NikolaTotev/Teensy-Balance-Bot-Mk_1/Documentation/Documentation Images/Microduino.png

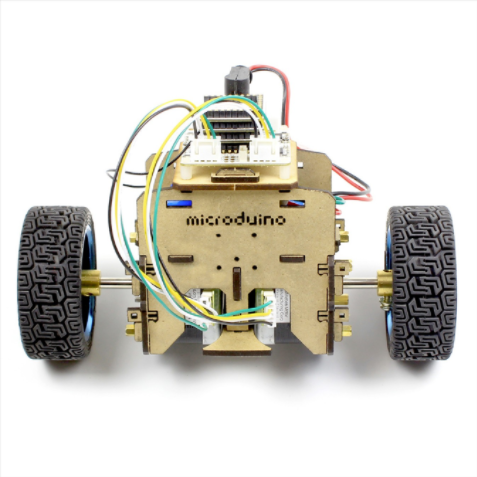
Documentation/Documentation Images/Microduino.png
