NikolaTotev/Teensy-Balance-Bot-Mk_1/Documentation/Images/Github_Cover.png

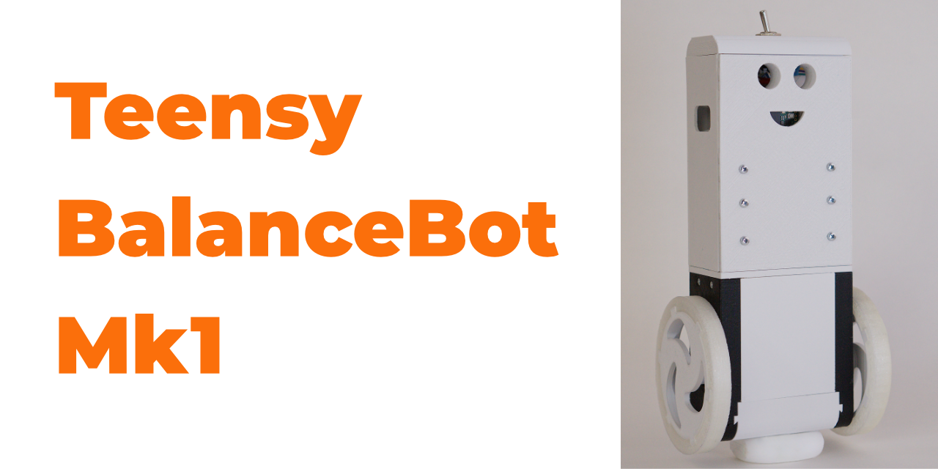
Documentation/Images/Github_Cover.png
