NikolaTotev/Teensy-Balance-Bot-Mk_1/Documentation/Presentation Images/3D Model.png

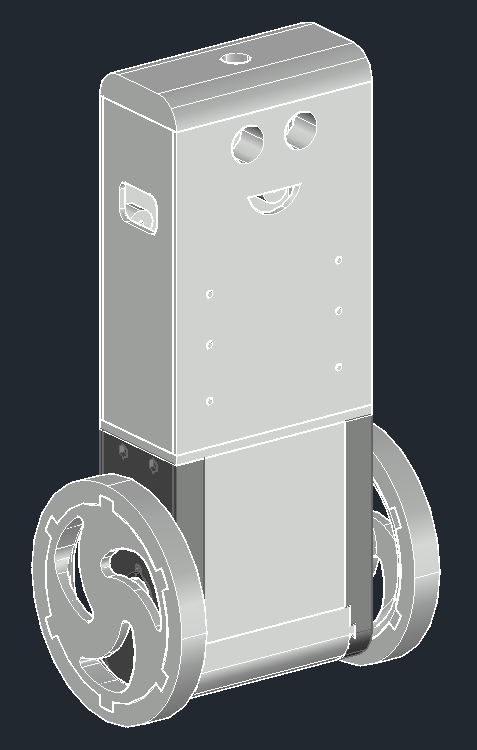
Documentation/Presentation Images/3D Model.png
