NikolaTotev/Teensy-Balance-Bot-Mk_1/Documentation/Presentation Images/2021-02-09 13_29_29-Pololu - Magnetic Encoder Pair Kit for Micro Metal Gearmotors, 12 CPR, 2.7-18V.png

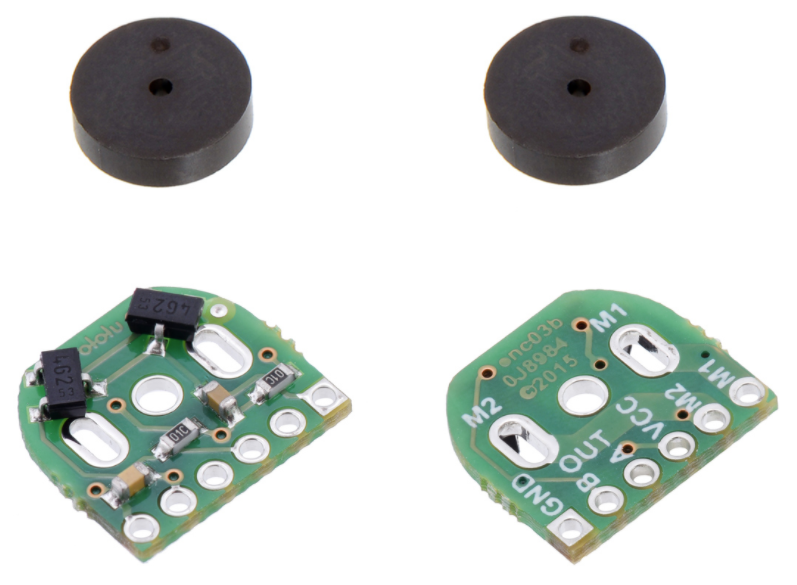
Documentation/Presentation Images/2021-02-09 13_29_29-Pololu - Magnetic Encoder Pair Kit for Micro Metal Gearmotors, 12 CPR, 2.7-18V.png
