NikolaTotev/Teensy-Balance-Bot-Mk_1/Documentation/Presentation Images/add_3_blue_1.png

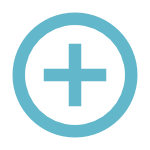
Documentation/Presentation Images/add_3_blue_1.png
