NikolaTotev/Teensy-Balance-Bot-Mk_1/Documentation/Presentation Images/Analysis.png

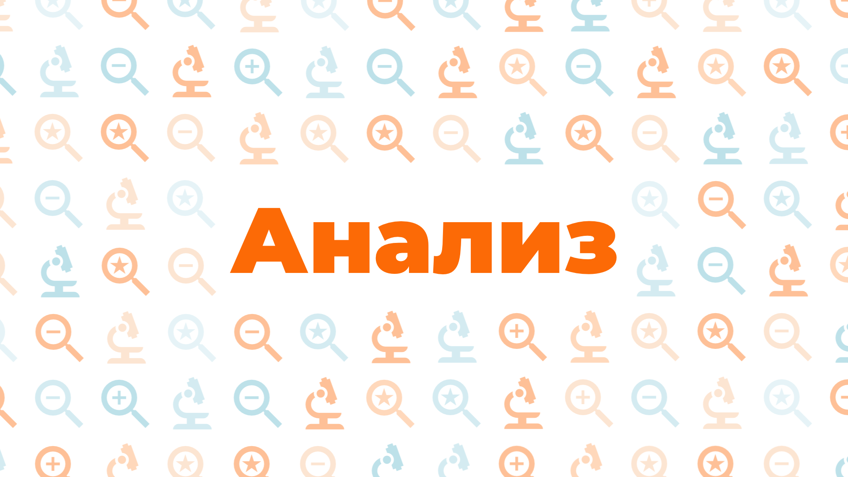
Documentation/Presentation Images/Analysis.png
