NikolaTotev/Teensy-Balance-Bot-Mk_1/Documentation/Presentation Images/Anl_Orange_1.png

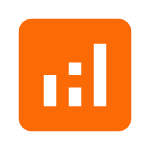
Documentation/Presentation Images/Anl_Orange_1.png
