NikolaTotev/Teensy-Balance-Bot-Mk_1/Documentation/Presentation Images/Batteries.png

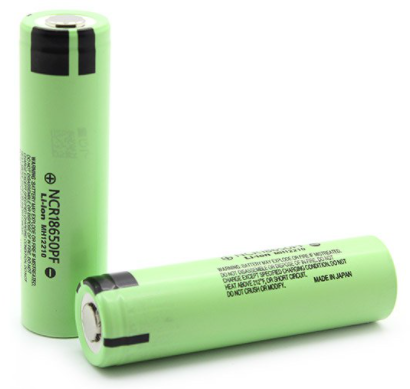
Documentation/Presentation Images/Batteries.png
