NikolaTotev/Teensy-Balance-Bot-Mk_1/Documentation/Presentation Images/Brand_Visual_Studio_Win_2019.png

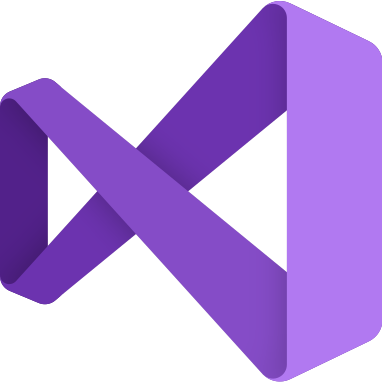
Documentation/Presentation Images/Brand_Visual_Studio_Win_2019.png
