NikolaTotev/Teensy-Balance-Bot-Mk_1/Documentation/Presentation Images/Calc_Orange_1.png

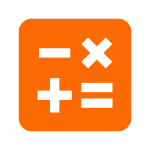
Documentation/Presentation Images/Calc_Orange_1.png
