NikolaTotev/Teensy-Balance-Bot-Mk_1/Documentation/Presentation Images/Check_Check_Blue_1.png

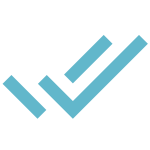
Documentation/Presentation Images/Check_Check_Blue_1.png
