NikolaTotev/Teensy-Balance-Bot-Mk_1/Documentation/Presentation Images/con_blue2.png

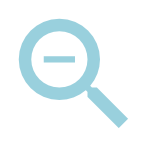
Documentation/Presentation Images/con_blue2.png
