NikolaTotev/Teensy-Balance-Bot-Mk_1/Documentation/Presentation Images/Development.png

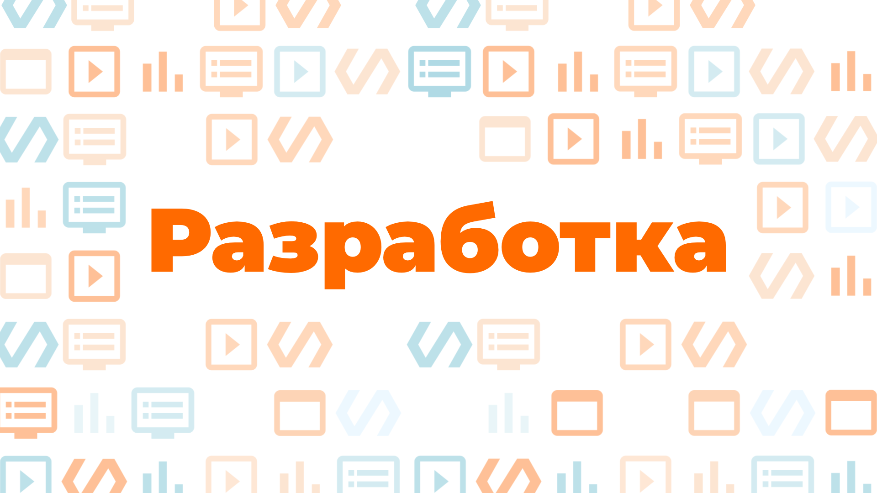
Documentation/Presentation Images/Development.png
