NikolaTotev/Teensy-Balance-Bot-Mk_1/Documentation/Presentation Images/edit_blue_1.png

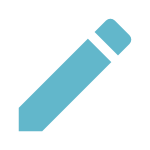
Documentation/Presentation Images/edit_blue_1.png
