NikolaTotev/Teensy-Balance-Bot-Mk_1/Documentation/Presentation Images/examine_blue_1.png

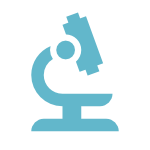
Documentation/Presentation Images/examine_blue_1.png
