NikolaTotev/Teensy-Balance-Bot-Mk_1/Documentation/Presentation Images/Feature_2_orange_1.png

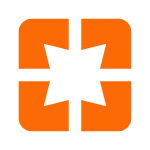
Documentation/Presentation Images/Feature_2_orange_1.png
