NikolaTotev/Teensy-Balance-Bot-Mk_1/Documentation/Presentation Images/Func_Orange_1.png

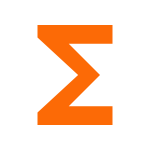
Documentation/Presentation Images/Func_Orange_1.png
