NikolaTotev/Teensy-Balance-Bot-Mk_1/Documentation/Presentation Images/Functionality.png

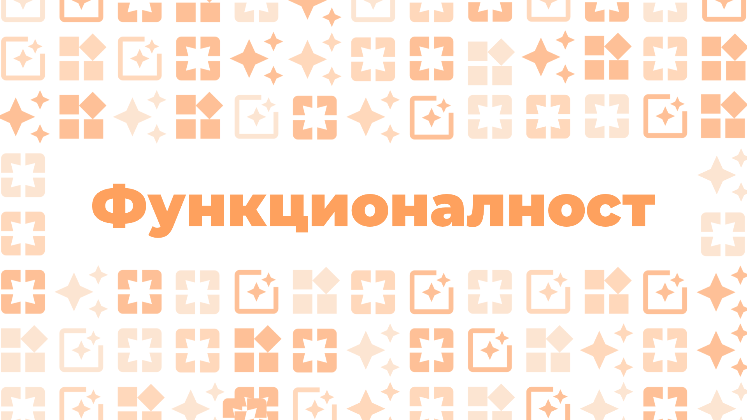
Documentation/Presentation Images/Functionality.png
