NikolaTotev/Teensy-Balance-Bot-Mk_1/Documentation/Presentation Images/Future.png

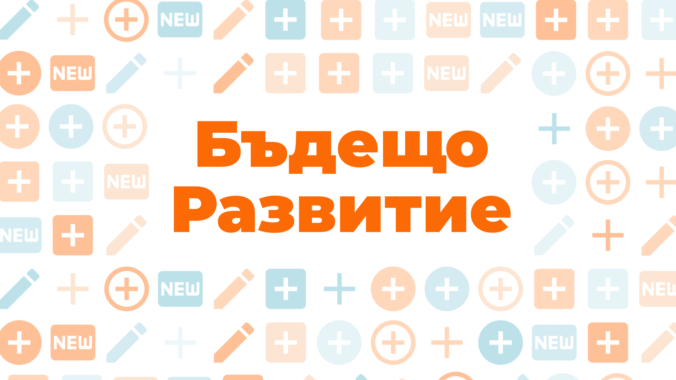
Documentation/Presentation Images/Future.png
