NikolaTotev/Teensy-Balance-Bot-Mk_1/Documentation/Presentation Images/Grading_Blue_1.png

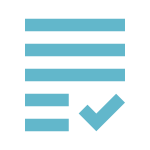
Documentation/Presentation Images/Grading_Blue_1.png
