NikolaTotev/Teensy-Balance-Bot-Mk_1/Documentation/Presentation Images/Grading_Blue_2.png

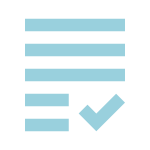
Documentation/Presentation Images/Grading_Blue_2.png
