NikolaTotev/Teensy-Balance-Bot-Mk_1/Documentation/Presentation Images/Gyro.png

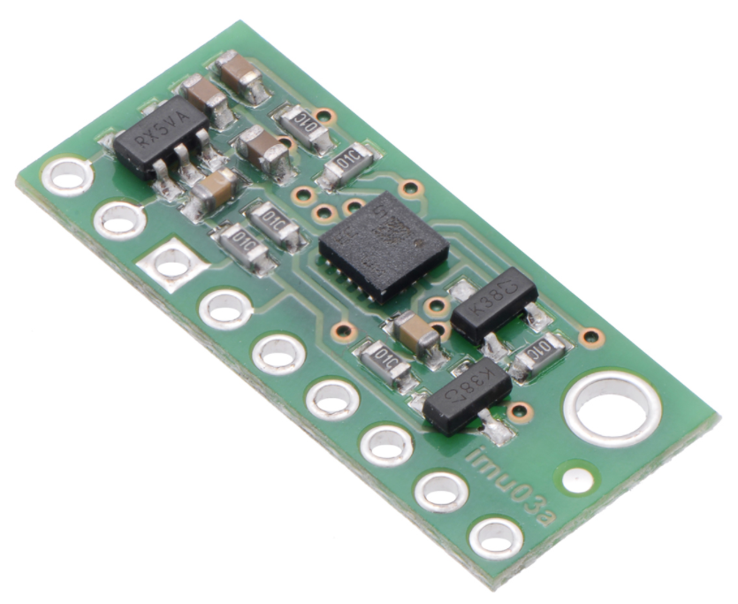
Documentation/Presentation Images/Gyro.png
