NikolaTotev/Teensy-Balance-Bot-Mk_1/Documentation/Presentation Images/help_1_orange_1.png

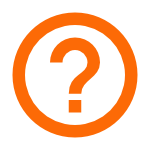
Documentation/Presentation Images/help_1_orange_1.png
