NikolaTotev/Teensy-Balance-Bot-Mk_1/Documentation/Presentation Images/help_1_orange_3.png

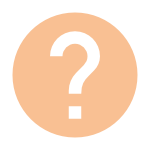
Documentation/Presentation Images/help_1_orange_3.png
