NikolaTotev/Teensy-Balance-Bot-Mk_1/Documentation/Presentation Images/help_orange_1.png

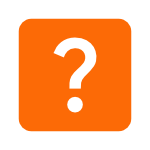
Documentation/Presentation Images/help_orange_1.png
