NikolaTotev/Teensy-Balance-Bot-Mk_1/Documentation/Presentation Images/Lab_Blue_1.png

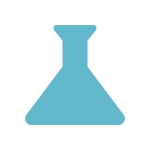
Documentation/Presentation Images/Lab_Blue_1.png
