NikolaTotev/Teensy-Balance-Bot-Mk_1/Documentation/Presentation Images/MATLAB-Emblema.png

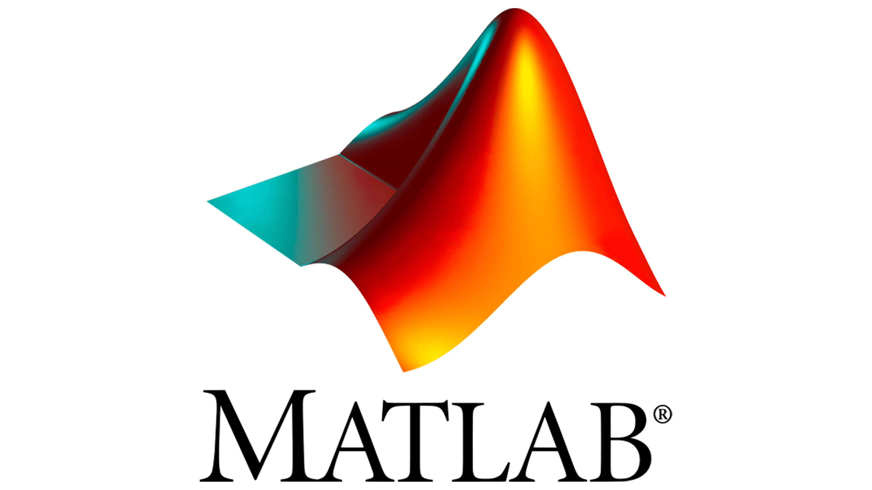
Documentation/Presentation Images/MATLAB-Emblema.png
