NikolaTotev/Teensy-Balance-Bot-Mk_1/Documentation/Presentation Images/Mod_Orange_1.png

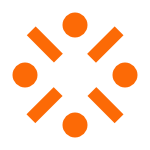
Documentation/Presentation Images/Mod_Orange_1.png
