NikolaTotev/Teensy-Balance-Bot-Mk_1/Documentation/Presentation Images/Model.png

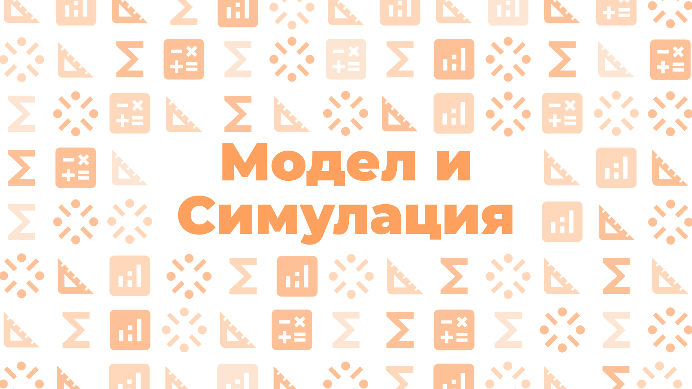
Documentation/Presentation Images/Model.png
