NikolaTotev/Teensy-Balance-Bot-Mk_1/Documentation/Presentation Images/MotorDriver.png

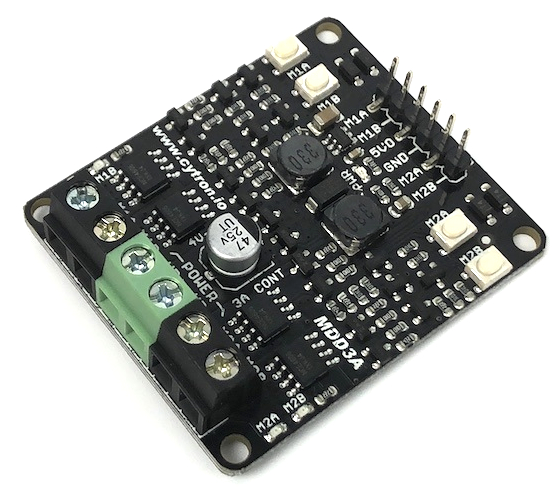
Documentation/Presentation Images/MotorDriver.png
