NikolaTotev/Teensy-Balance-Bot-Mk_1/Documentation/Presentation Images/Motors.png

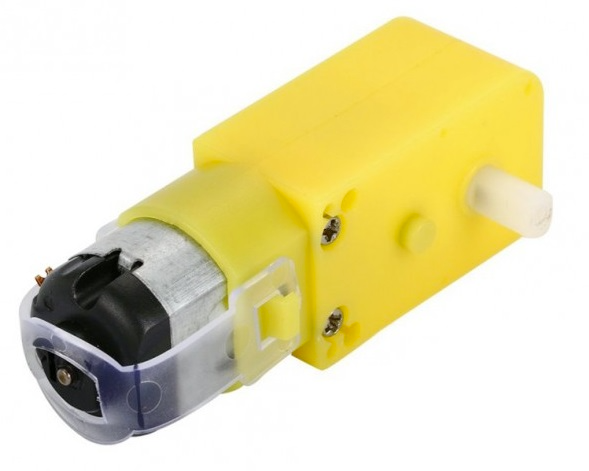
Documentation/Presentation Images/Motors.png
