NikolaTotev/Teensy-Balance-Bot-Mk_1/Documentation/Presentation Images/new_blue_1.png

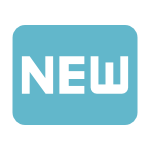
Documentation/Presentation Images/new_blue_1.png
