NikolaTotev/Teensy-Balance-Bot-Mk_1/Documentation/Presentation Images/Pass_Blue_1.png

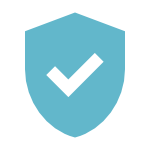
Documentation/Presentation Images/Pass_Blue_1.png
