NikolaTotev/Teensy-Balance-Bot-Mk_1/Documentation/Presentation Images/unnamed.jpg

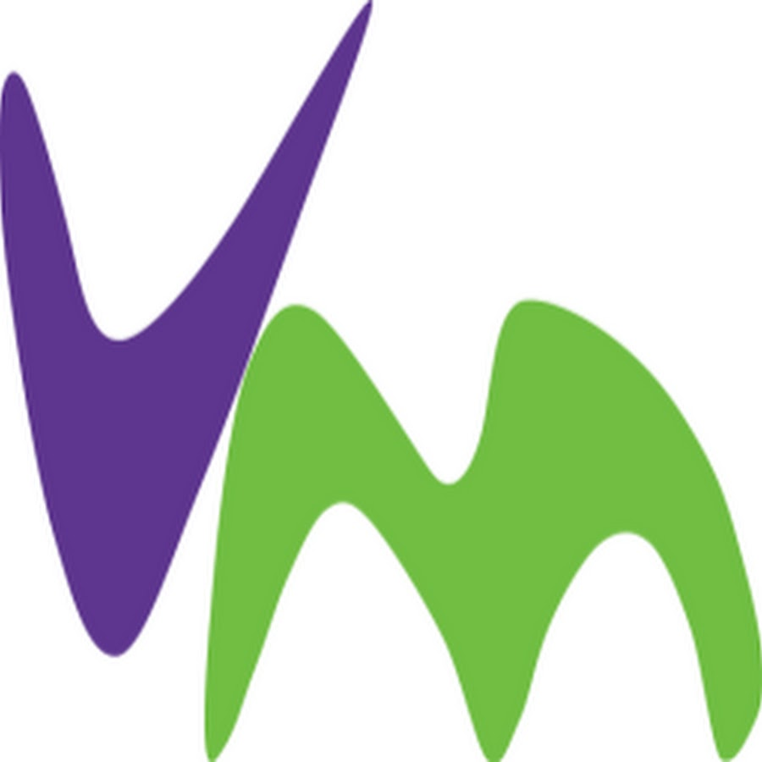
Documentation/Presentation Images/unnamed.jpg
