NikolaTotev/Teensy-Balance-Bot-Mk_1/Documentation/Presentation Images/Walkera-Furious-215-FPV-racing-drone-1.png

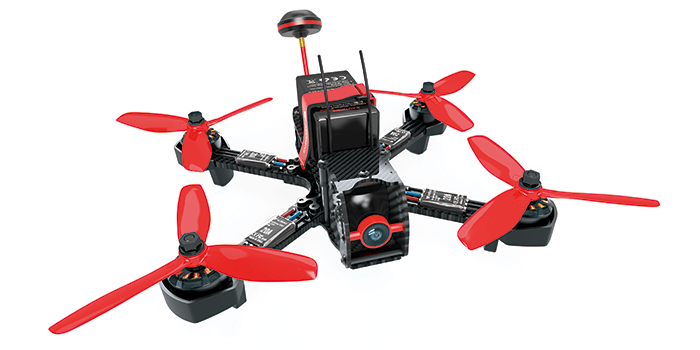
Documentation/Presentation Images/Walkera-Furious-215-FPV-racing-drone-1.png
