NikolaTotev/Teensy-Balance-Bot-Mk_1/Documentation/Presentation Images/What.png

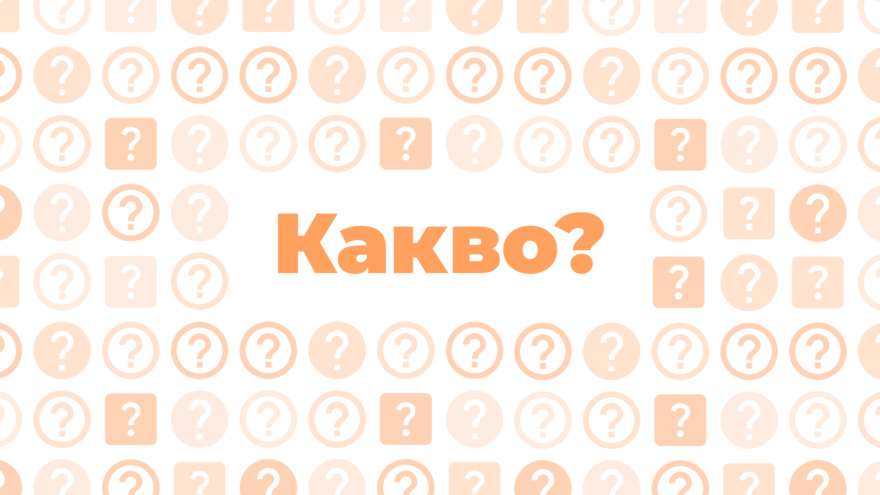
Documentation/Presentation Images/What.png
