NikolaTotev/Teensy-Balance-Bot-Mk_1/Documentation/Software Diagrams/Teensy BalanceBot Software Diagram.png

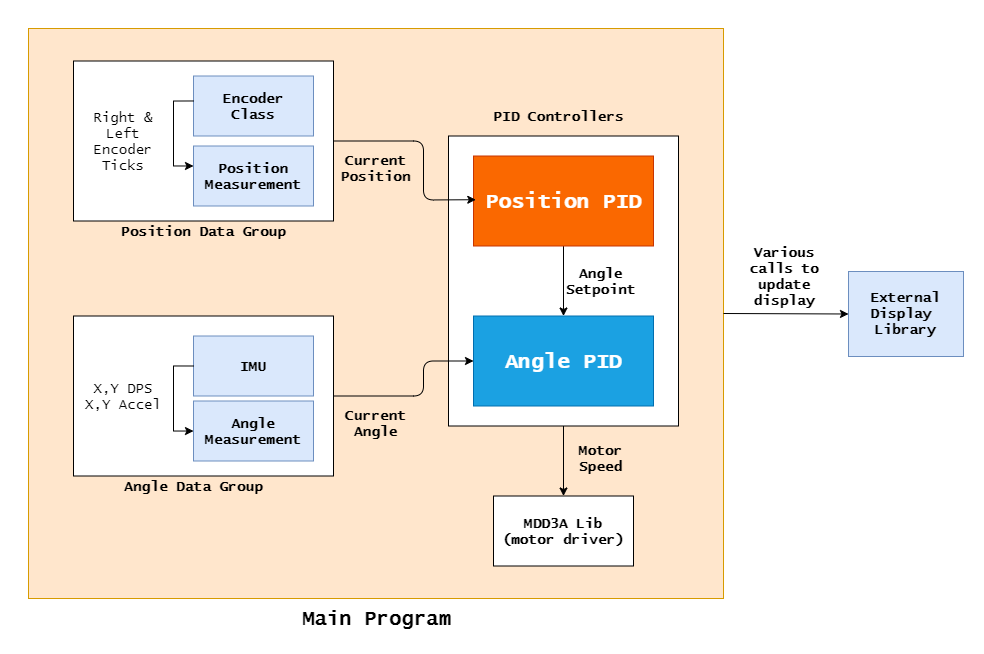
Documentation/Software Diagrams/Teensy BalanceBot Software Diagram.png
