NikolaTotev/Teensy-Balance-Bot-Mk_1/Documentation/Video/BalanceBot Demo Video Thumbnail.png

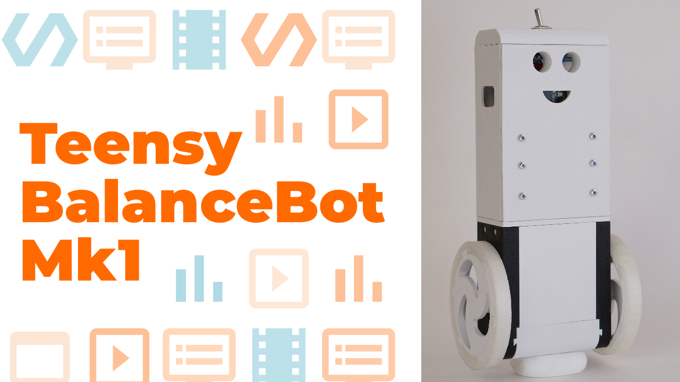
Documentation/Video/BalanceBot Demo Video Thumbnail.png
