NikolaTotev/Teensy-Balance-Bot-Mk_1/STL Files/Battery_Compartment.stl

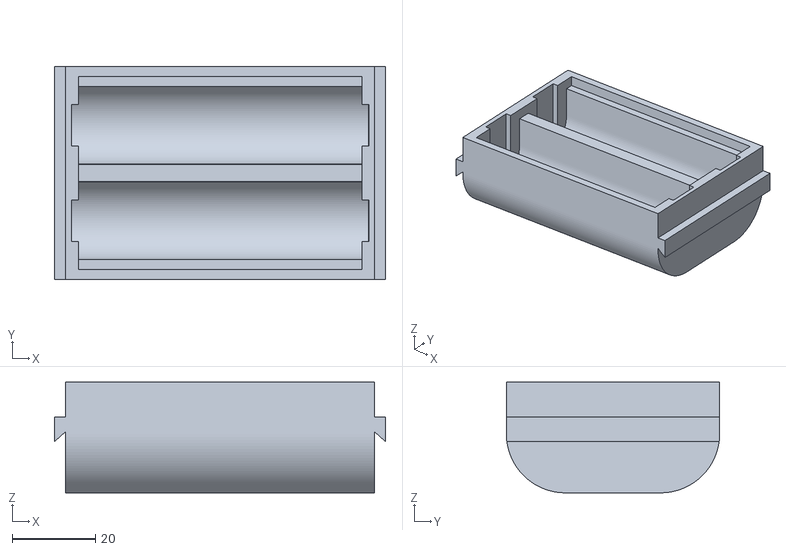
[picture p106: CAD file, 2020-12-08]
STL Files/Battery_Compartment.stl
79.6 x 51.3 x 26.6
