NikolaTotev/Teensy-Balance-Bot-Mk_1/STL Files/Left_Side_Panel.stl

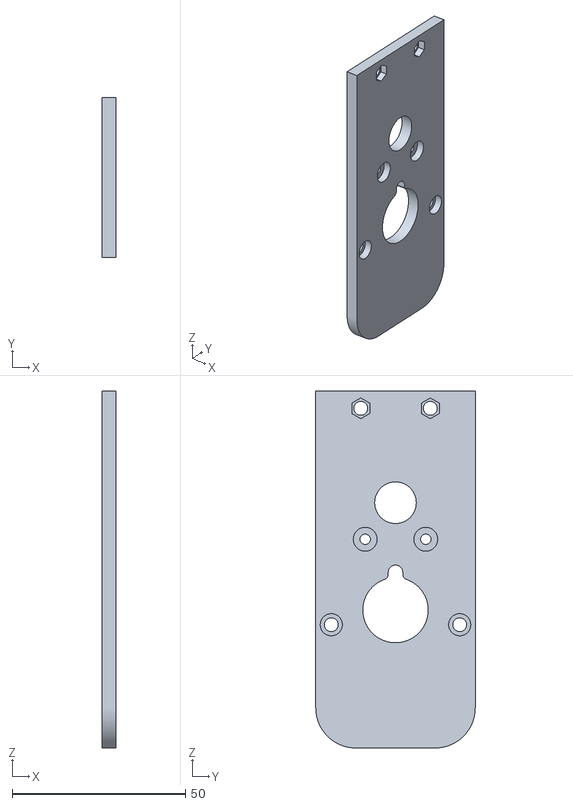
[picture p107: CAD file, 2020-12-08]
STL Files/Left_Side_Panel.stl
4.00 x 46.0 x 103.0
