NikolaTotev/Teensy-Balance-Bot-Mk_1/STL Files/Positive_Batt_Spring.stl

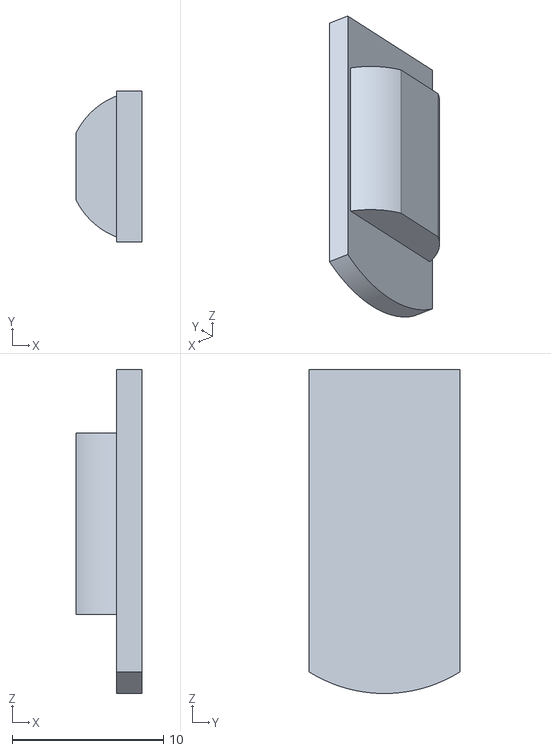
[picture p108: CAD file, 2020-12-08]
STL Files/Positive_Batt_Spring.stl
4.39 x 10.0 x 21.4
