NikolaTotev/Teensy-Balance-Bot-Mk_1/STL Files/Right_Panel_Mount.stl

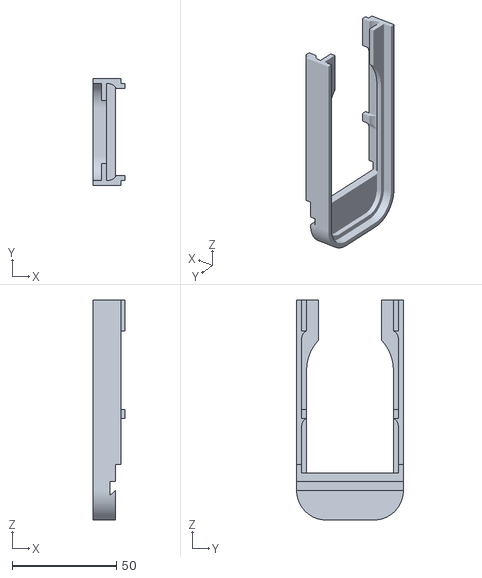
[picture p109: CAD file, 2020-12-08]
STL Files/Right_Panel_Mount.stl
15.4 x 51.3 x 105.6
