NikolaTotev/Teensy-Balance-Bot-Mk_1/STL Files/Middle_Panel.stl

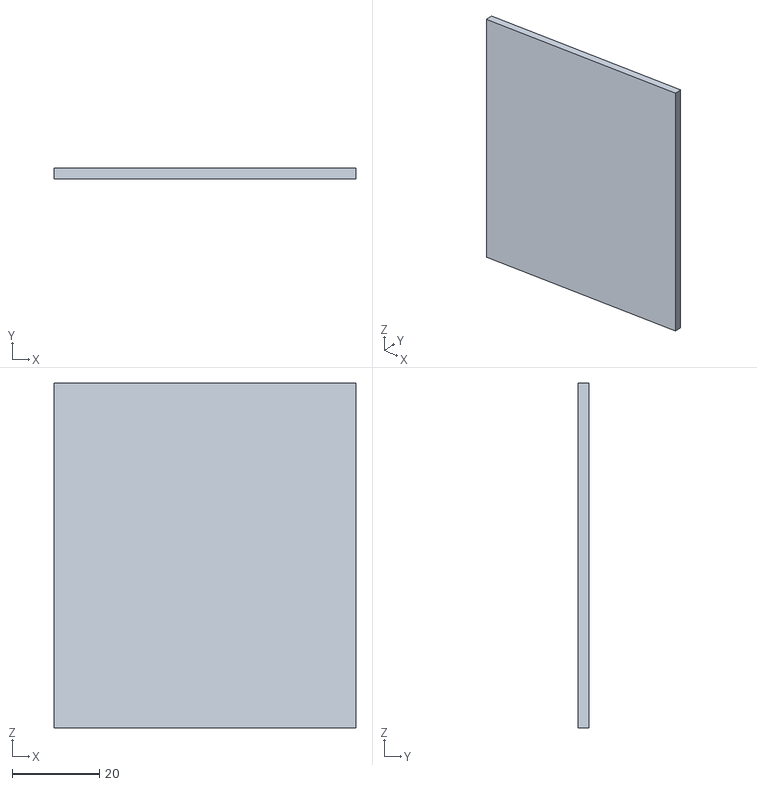
[picture p110: CAD file, 2020-12-08]
STL Files/Middle_Panel.stl
69.1 x 2.42 x 79.0
