NikolaTotev/Teensy-Balance-Bot-Mk_1/Documentation/Presentation Images/Measure_Orange_1.png

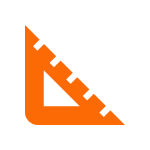
Documentation/Presentation Images/Measure_Orange_1.png
