NikolaTotev/Teensy-Balance-Bot-Mk_1/Documentation/Presentation Images/Testing.png

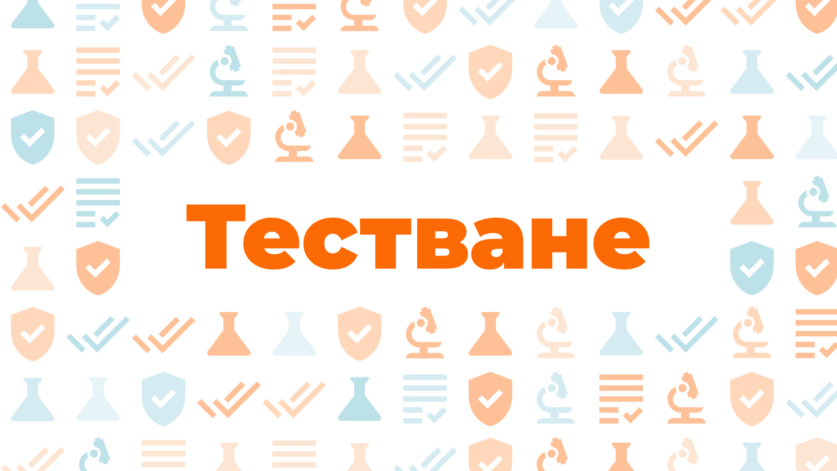
Documentation/Presentation Images/Testing.png
