NikolaTotev/Teensy-Balance-Bot-Mk_1/Source Code/Teensy_Balancing_Bot_Mk_1/Teensy_Balancing_Bot_Mk_1/Position.h

// Position.h

#ifndef _POSITION_h
#define _POSITION_h

#if defined(ARDUINO) && ARDUINO >= 100
#include "arduino.h"
#include "Encoder_Lib.h"

enum SelectSide
{
	R,
	L
};

class Position
{

	const int ticksPerRevolution = 3;
	const int wheelRadius = 50; //Unit is mm


	int16_t prevLeftWheelPosition = 0;
	int16_t prevRightWheelPosition = 0;

	int16_t leftWheelPosition = 0;
	int16_t rightWheelPosition = 0;

	float prevLeftDistanceTraveled = 0;
	float prevRightDistanceTraveled = 0;

	float leftDistanceTraveled = 0;
	float rightDistanceTraveled = 0;

	//ToDo implement this.
	bool rightMovingForward = false;
	bool leftMovingForward = false;

	Encoder *encoders;

	public:
	void calcRevolutions();
	void calcTravelDistance();

	Position(Encoder *encs)
	{
		encoders = encs;	
	}
	//This void is called by the main program loop.
	void Update();
	
	float GetLeftEstimagedDistance();
	float GetRighttEstimagedDistance();
	int16_t RW_GetEstimatedPosition();
	int16_t LW_GetEstimatedPosition();

};
#else
#include "WProgram.h"
#endif


#endif
